PrietoGodinoLab/OptoPi/OptoPi V1/Photos/IMG_20220902_123817.jpg

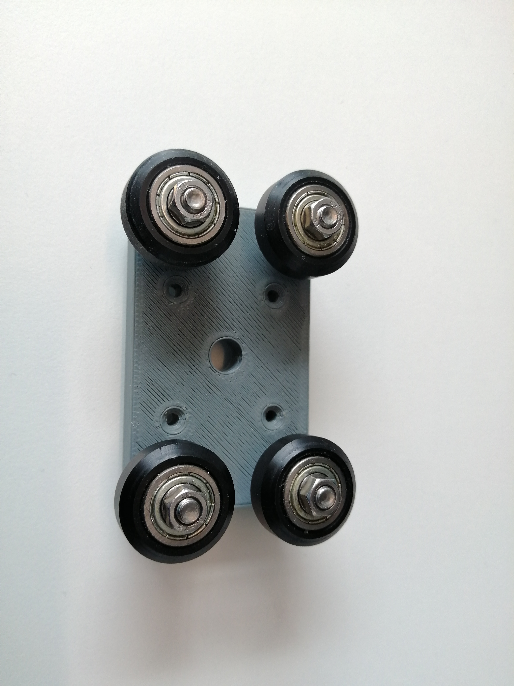
OptoPi V1/Photos/IMG_20220902_123817.jpg
