PrietoGodinoLab/OptoPi/OptoPi V1/Photos/IMG_20220902_124619.jpg

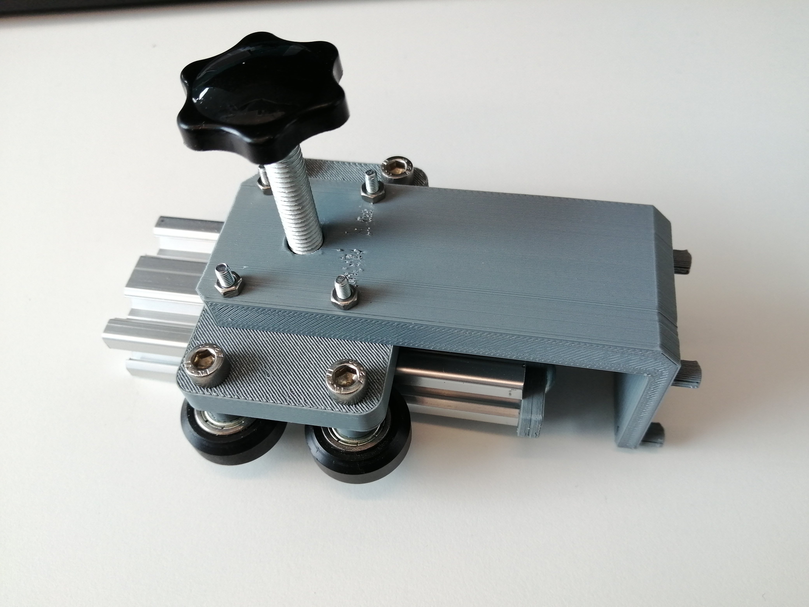
OptoPi V1/Photos/IMG_20220902_124619.jpg
