PrietoGodinoLab/OptoPi/OptoPi V1/Photos/IMG_20220927_121345.jpg

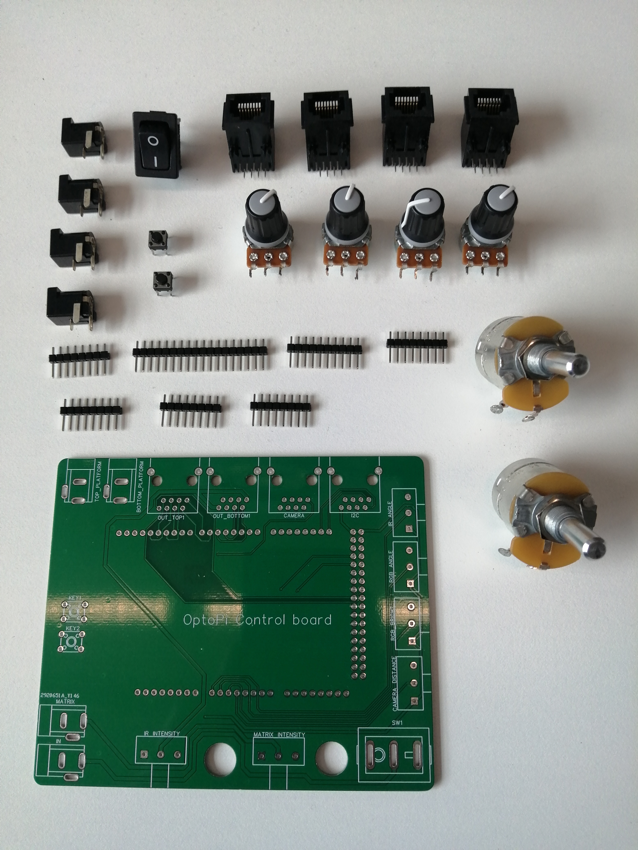
OptoPi V1/Photos/IMG_20220927_121345.jpg
