PrietoGodinoLab/OptoPi/OptoPi V1/Photos/IMG_20220929_140732.jpg

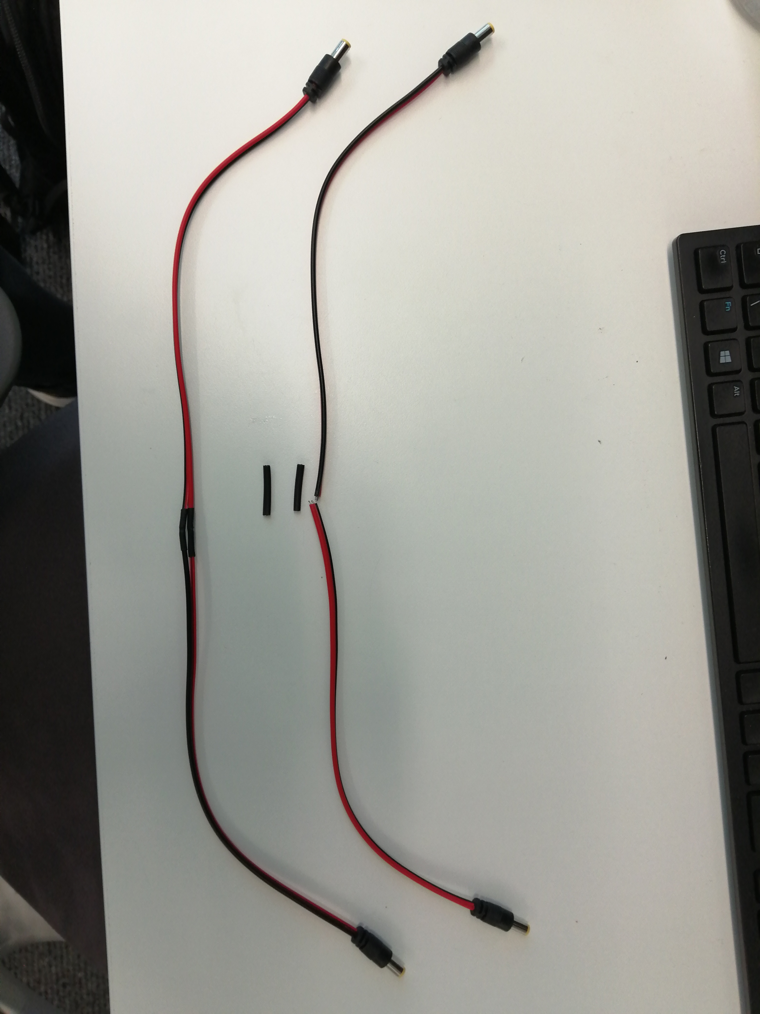
OptoPi V1/Photos/IMG_20220929_140732.jpg
