PrietoGodinoLab/OptoPi/OptoPi V1/Photos/IMG_20220929_161415.jpg

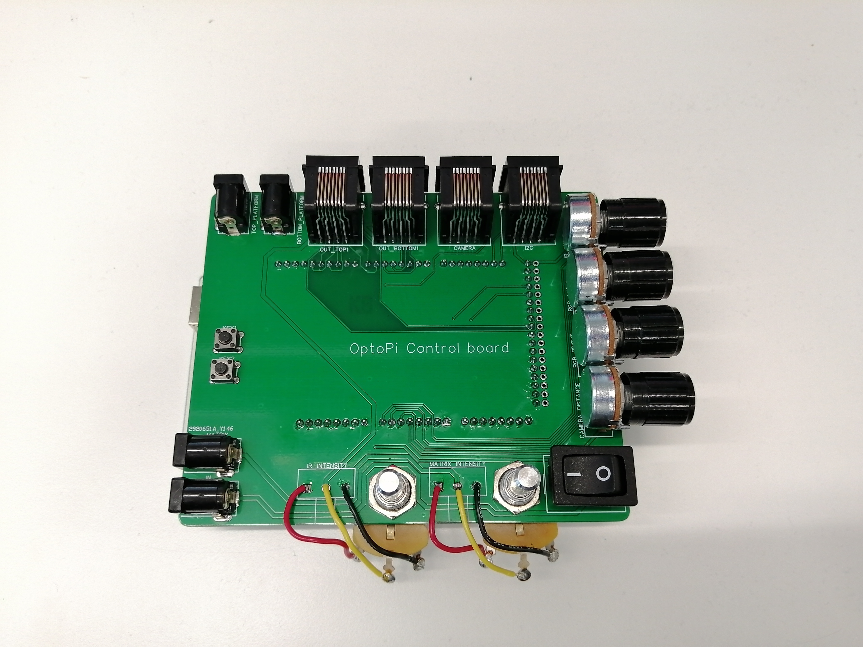
OptoPi V1/Photos/IMG_20220929_161415.jpg
