PrietoGodinoLab/OptoPi/OptoPi V1/Photos/IMG_20221003_110427.jpg

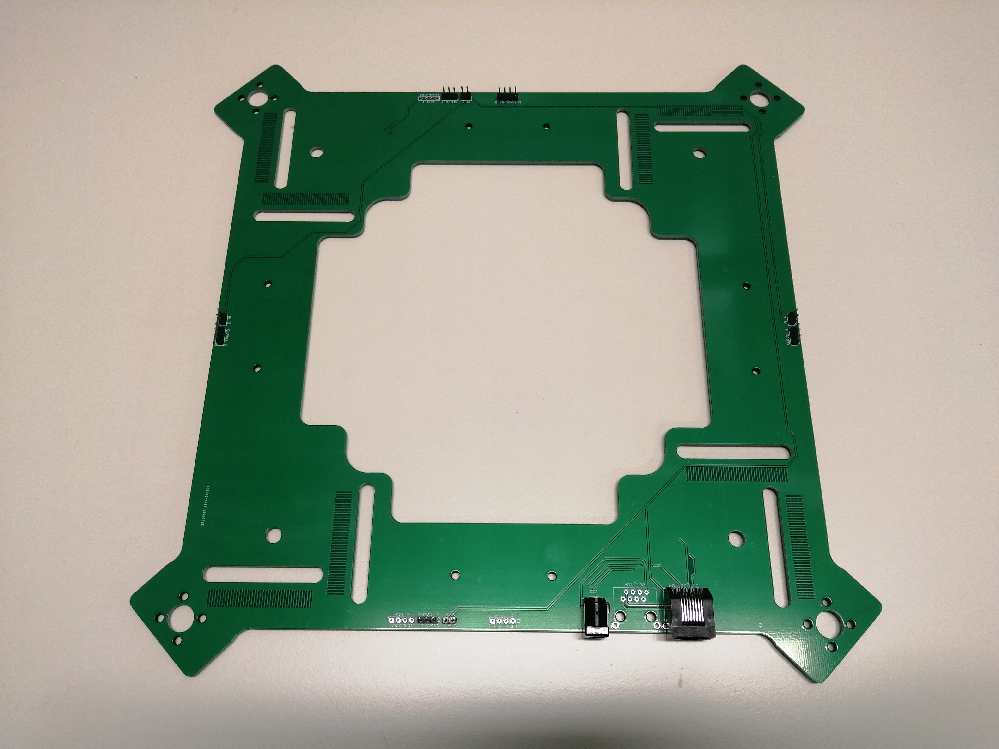
OptoPi V1/Photos/IMG_20221003_110427.jpg
