PrietoGodinoLab/OptoPi/OptoPi V1/Photos/IMG_20221003_110507.jpg

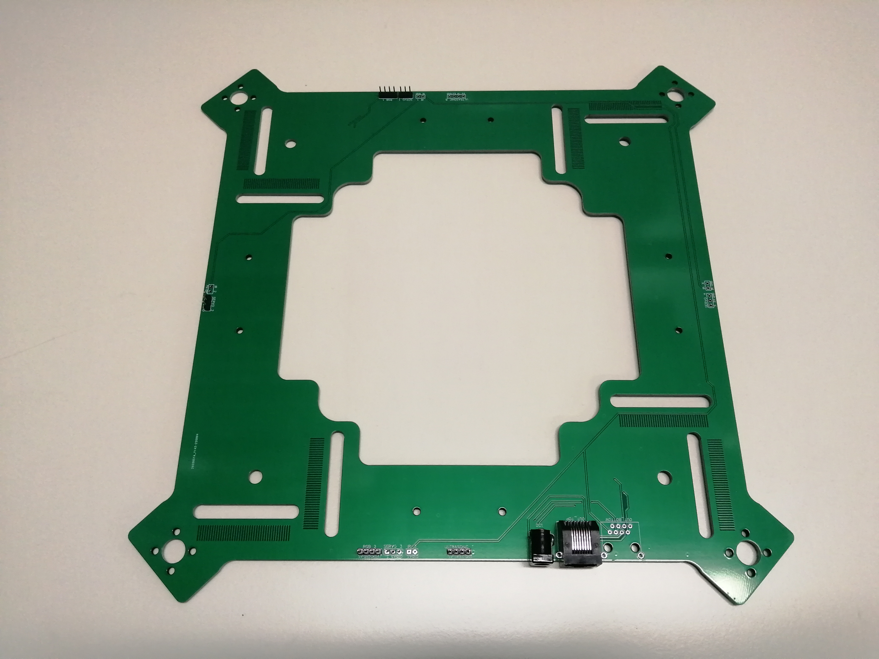
OptoPi V1/Photos/IMG_20221003_110507.jpg
