PrietoGodinoLab/OptoPi/OptoPi V1/Photos/IMG_20221003_115522.jpg

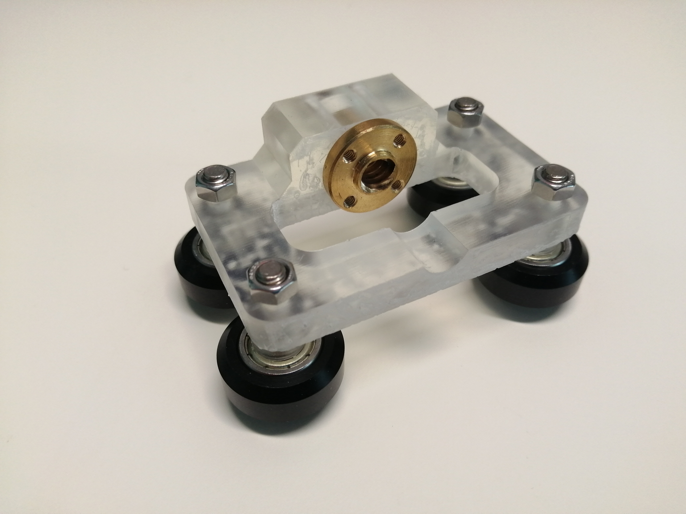
OptoPi V1/Photos/IMG_20221003_115522.jpg
