PrietoGodinoLab/OptoPi/OptoPi V1/Photos/IMG_20221003_143128.jpg

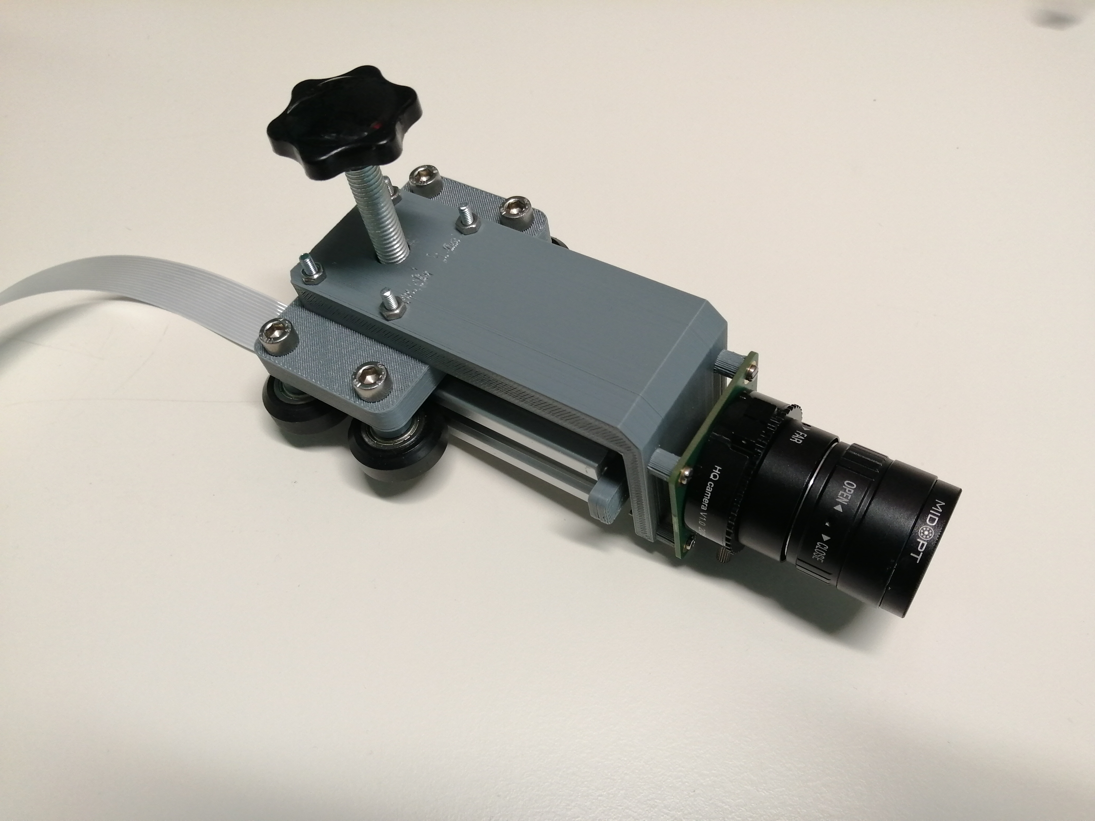
OptoPi V1/Photos/IMG_20221003_143128.jpg
