PrietoGodinoLab/OptoPi/OptoPi V1/Photos/IMG_20221003_161605.jpg

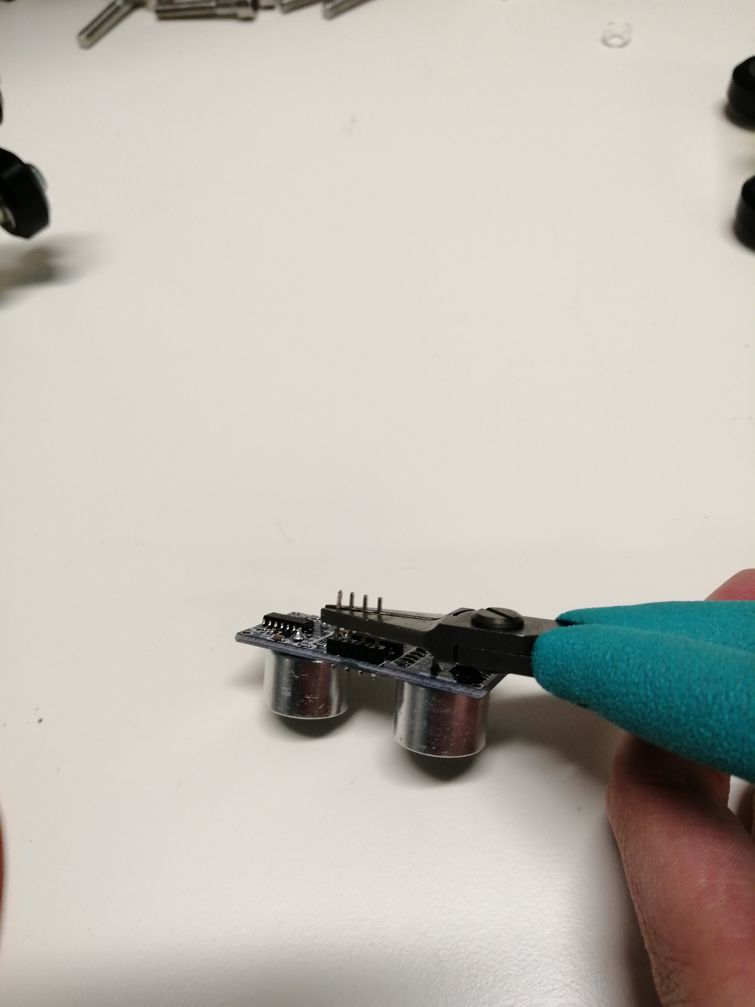
OptoPi V1/Photos/IMG_20221003_161605.jpg
