PrietoGodinoLab/OptoPi/OptoPi V1/Photos/IMG_20221004_111716.jpg

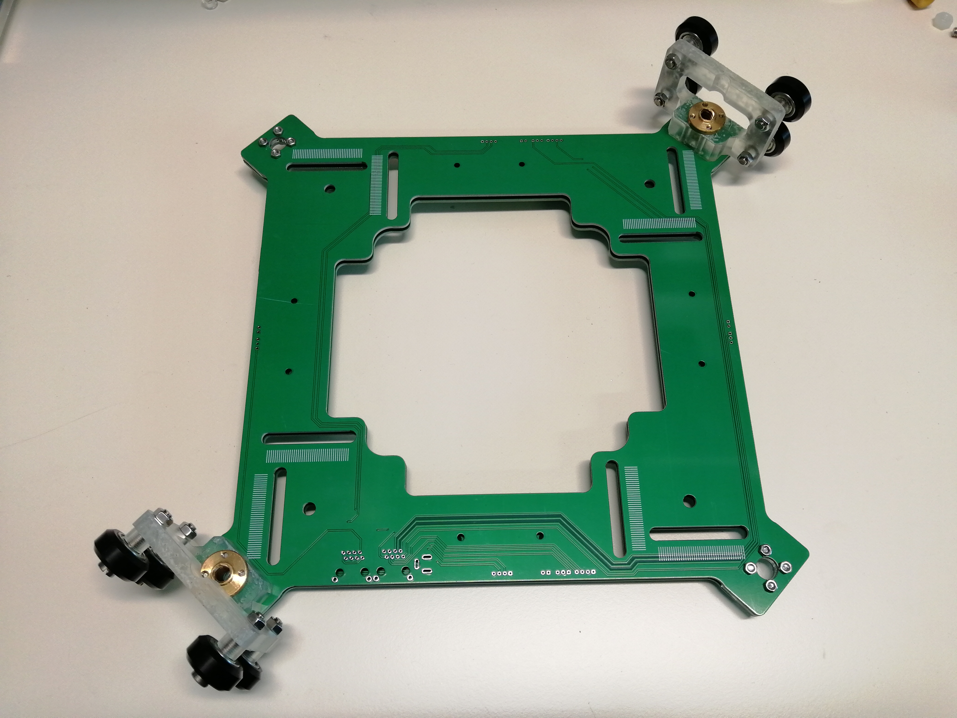
OptoPi V1/Photos/IMG_20221004_111716.jpg
