PrietoGodinoLab/OptoPi/OptoPi V1/Photos/IMG_20221004_111721_edit_144298494075898.jpg

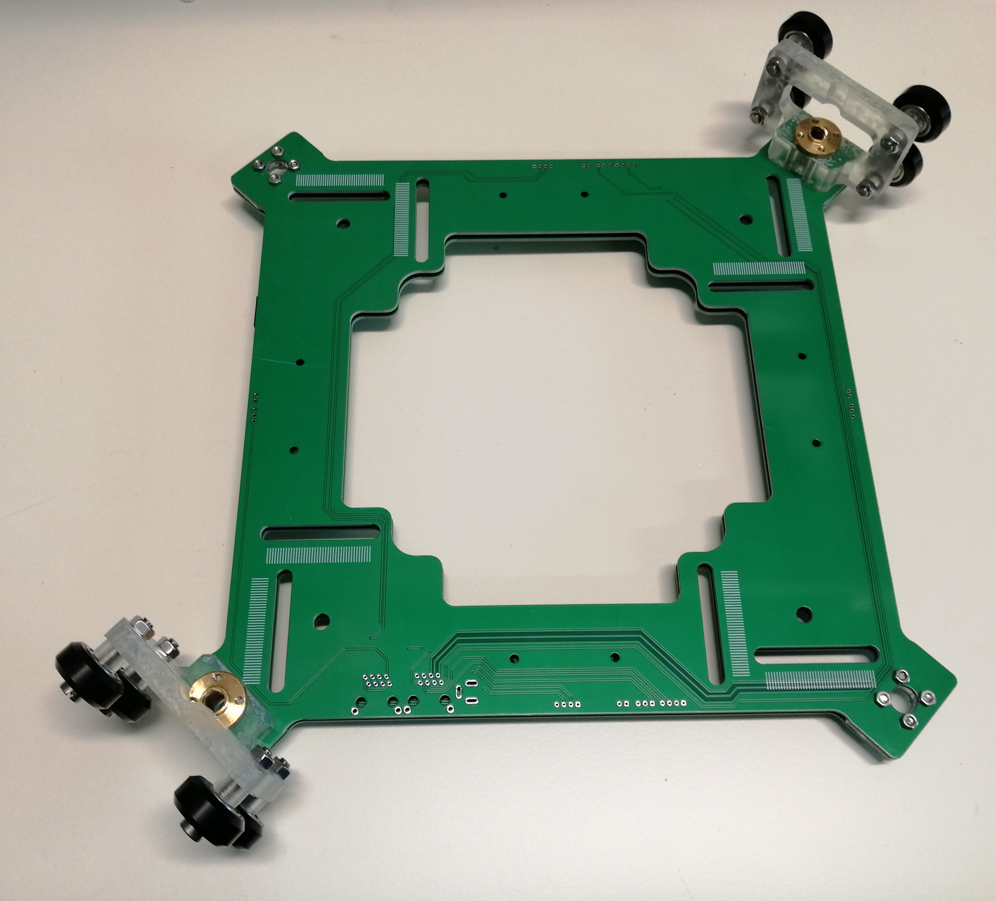
OptoPi V1/Photos/IMG_20221004_111721_edit_144298494075898.jpg
