PrietoGodinoLab/OptoPi/OptoPi V1/Photos/IMG_20221004_120927_edit_145196687061698.jpg

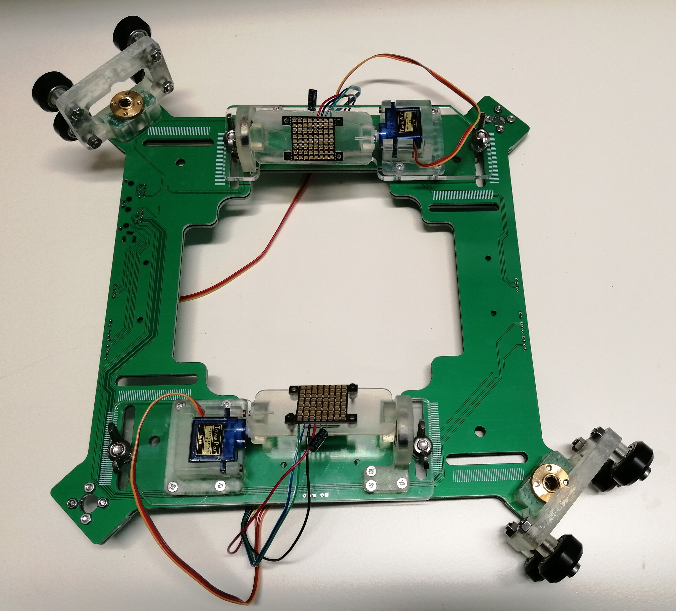
OptoPi V1/Photos/IMG_20221004_120927_edit_145196687061698.jpg
