PrietoGodinoLab/OptoPi/OptoPi V1/Photos/IMG_20221004_121041_edit_145273111731999.jpg

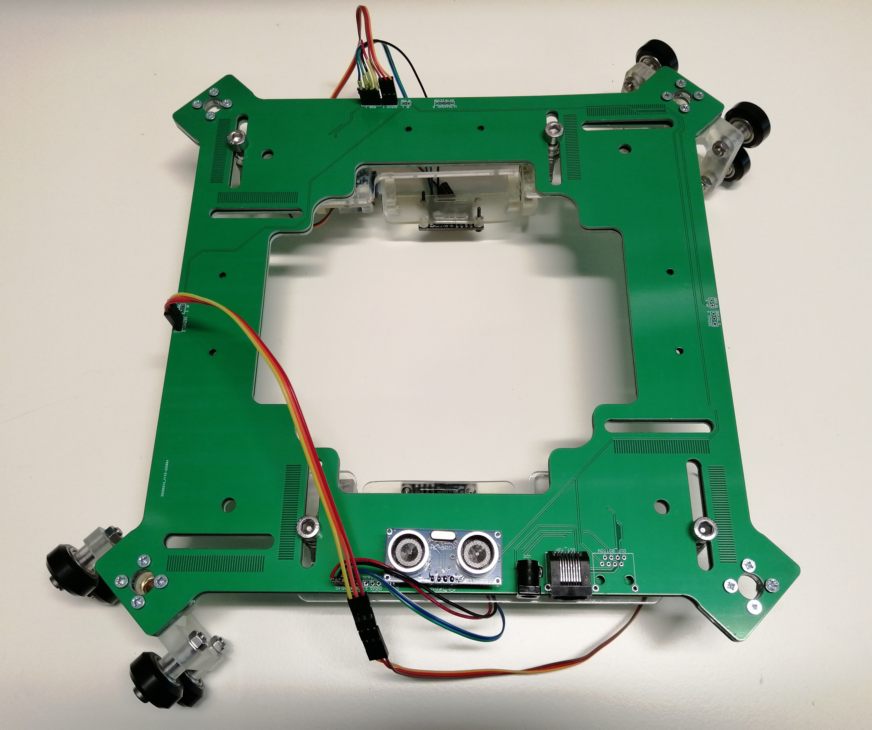
OptoPi V1/Photos/IMG_20221004_121041_edit_145273111731999.jpg
