PrietoGodinoLab/OptoPi/OptoPi V1/Photos/IMG_20221004_122243.jpg

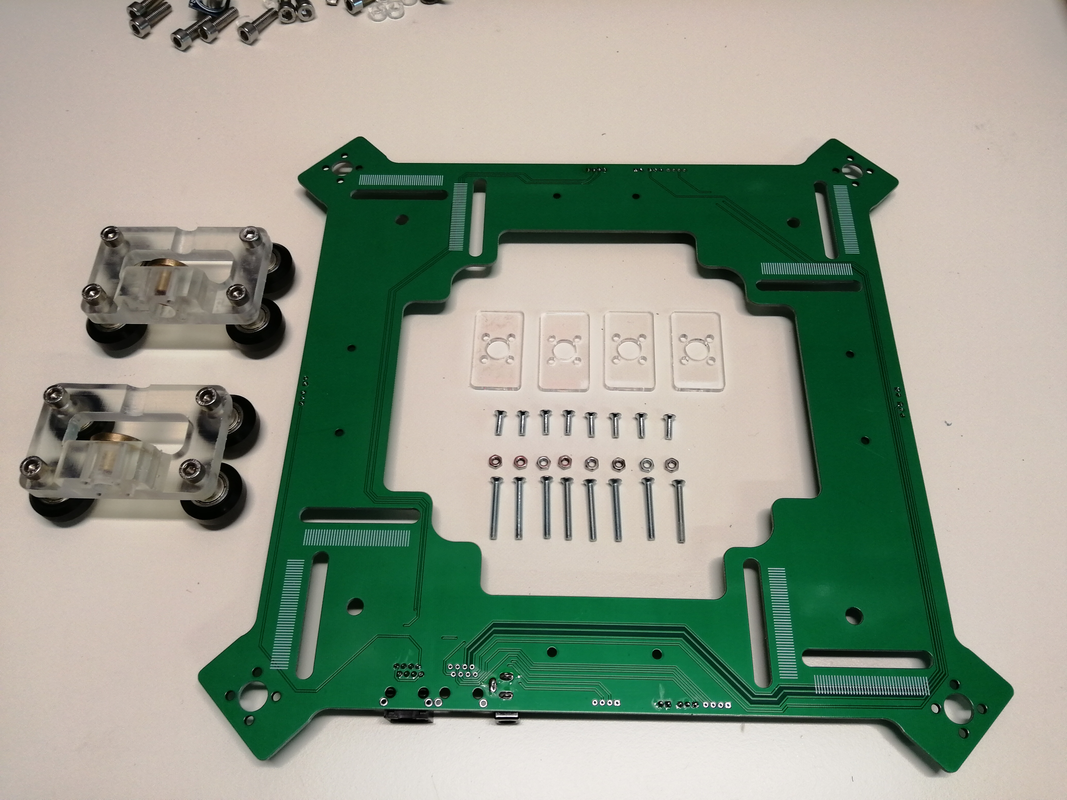
OptoPi V1/Photos/IMG_20221004_122243.jpg
