PrietoGodinoLab/OptoPi/OptoPi V1/Photos/IMG_20221004_122329_edit_145474023625718.jpg

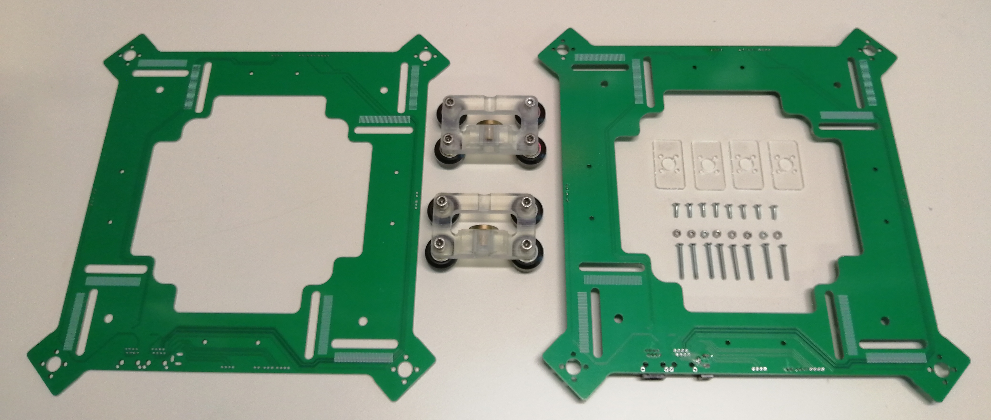
OptoPi V1/Photos/IMG_20221004_122329_edit_145474023625718.jpg
