PrietoGodinoLab/OptoPi/OptoPi V1/Photos/IMG_20221004_122958.jpg

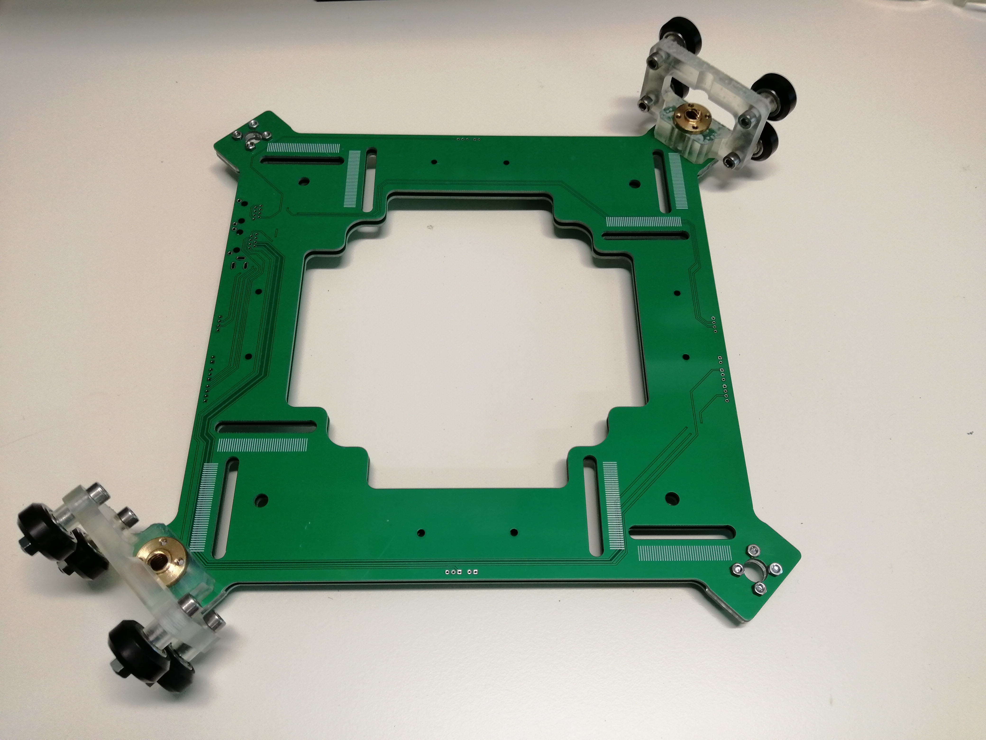
OptoPi V1/Photos/IMG_20221004_122958.jpg
