PrietoGodinoLab/OptoPi/OptoPi V1/Photos/IMG_20221004_123710.jpg

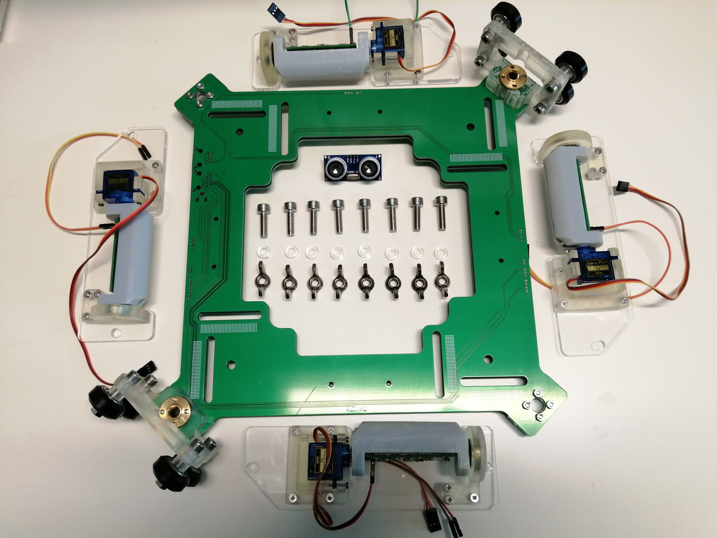
OptoPi V1/Photos/IMG_20221004_123710.jpg
