PrietoGodinoLab/OptoPi/OptoPi V1/Photos/IMG_20221004_131331_edit_146869959492172.jpg

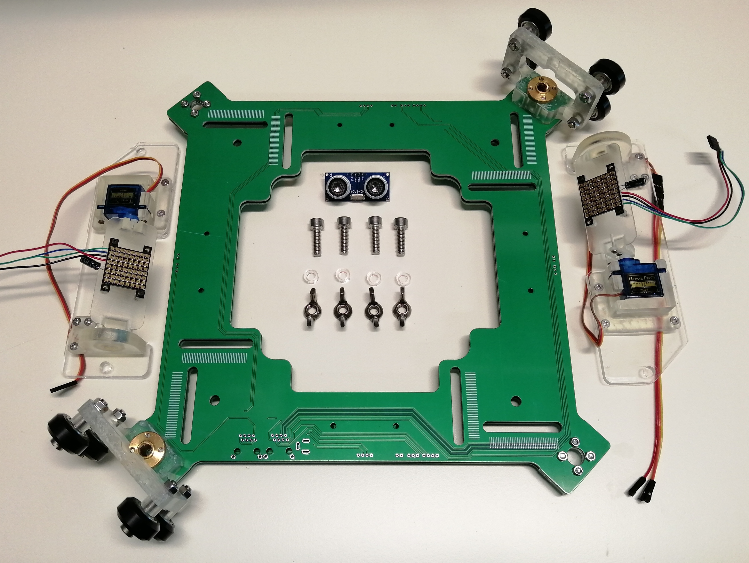
OptoPi V1/Photos/IMG_20221004_131331_edit_146869959492172.jpg
