PrietoGodinoLab/OptoPi/OptoPi V1/Photos/IMG_20221004_133414_edit_147019198305691.jpg

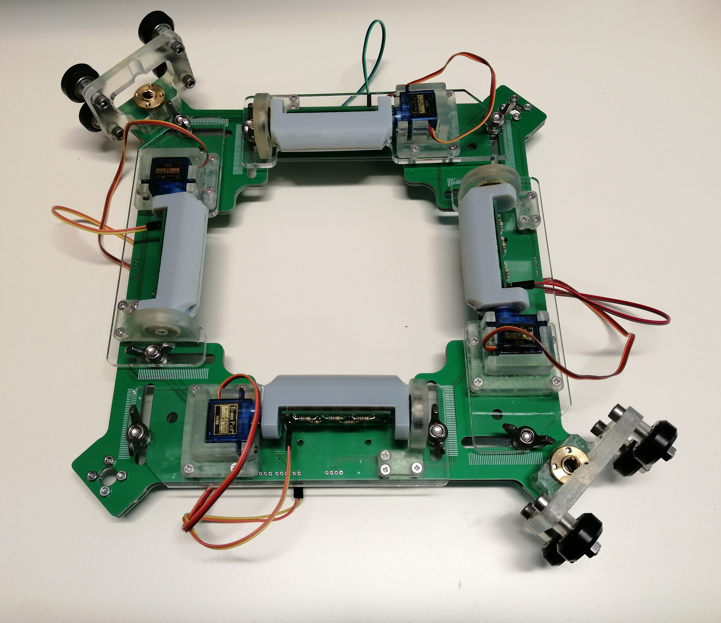
OptoPi V1/Photos/IMG_20221004_133414_edit_147019198305691.jpg
