PrietoGodinoLab/OptoPi/OptoPi V1/Photos/IMG_20221004_133534_edit_147065994163496.jpg

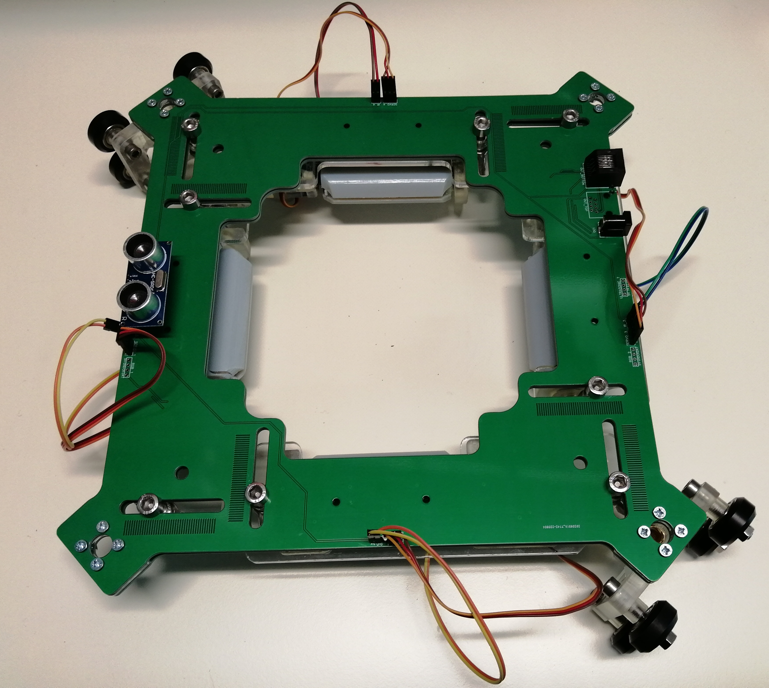
OptoPi V1/Photos/IMG_20221004_133534_edit_147065994163496.jpg
