PrietoGodinoLab/OptoPi/OptoPi V1/Photos/IMG_20221004_133632.jpg

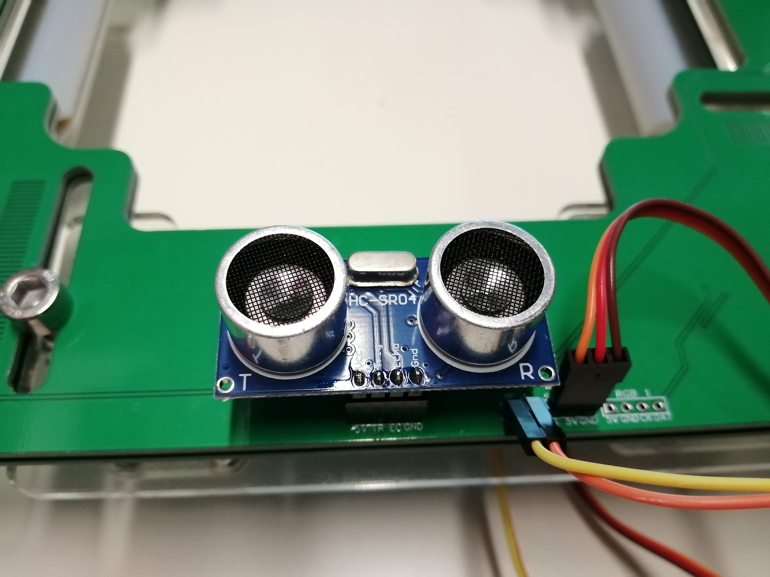
OptoPi V1/Photos/IMG_20221004_133632.jpg
