PrietoGodinoLab/OptoPi/OptoPi V1/Photos/IMG_20221005_123752.jpg

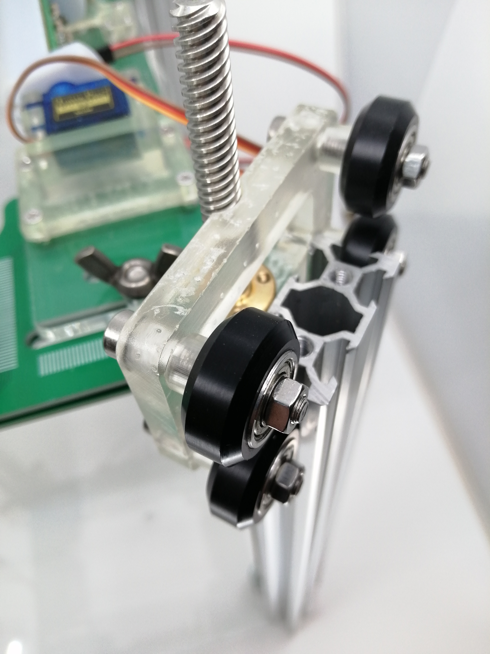
OptoPi V1/Photos/IMG_20221005_123752.jpg
