PrietoGodinoLab/OptoPi/OptoPi V1/Photos/IMG_20221005_123757.jpg

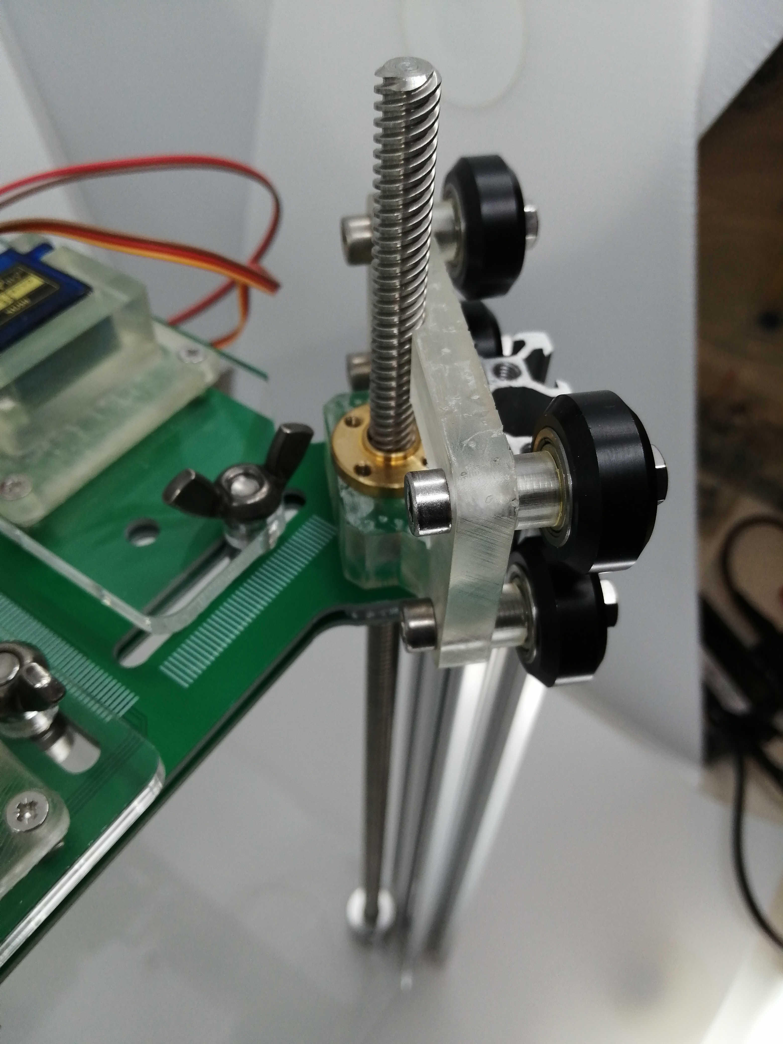
OptoPi V1/Photos/IMG_20221005_123757.jpg
