PrietoGodinoLab/OptoPi/OptoPi V1/Photos/IMG_20221005_123804.jpg

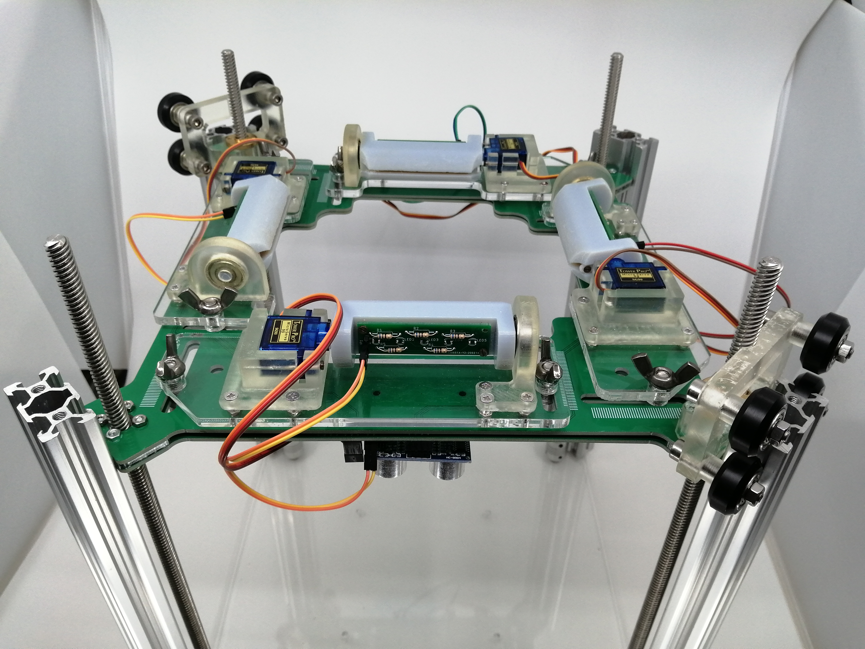
OptoPi V1/Photos/IMG_20221005_123804.jpg
