PrietoGodinoLab/OptoPi/OptoPi V1/Photos/IMG_20221005_123850.jpg

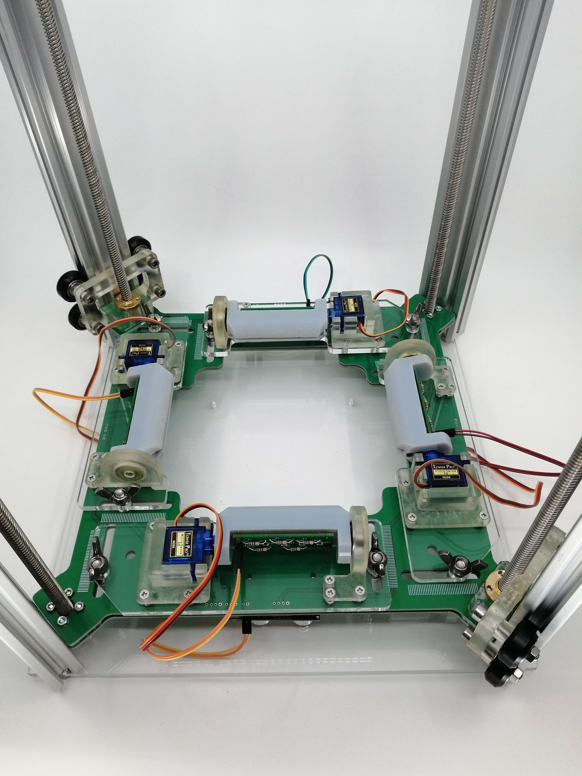
OptoPi V1/Photos/IMG_20221005_123850.jpg
