PrietoGodinoLab/OptoPi/OptoPi V1/Photos/IMG_20221005_124210.jpg

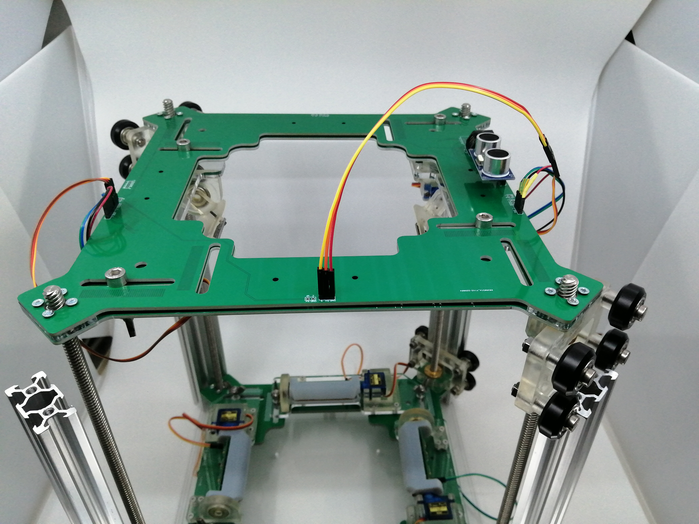
OptoPi V1/Photos/IMG_20221005_124210.jpg
