PrietoGodinoLab/OptoPi/OptoPi V1/Photos/IMG_20221005_124215.jpg

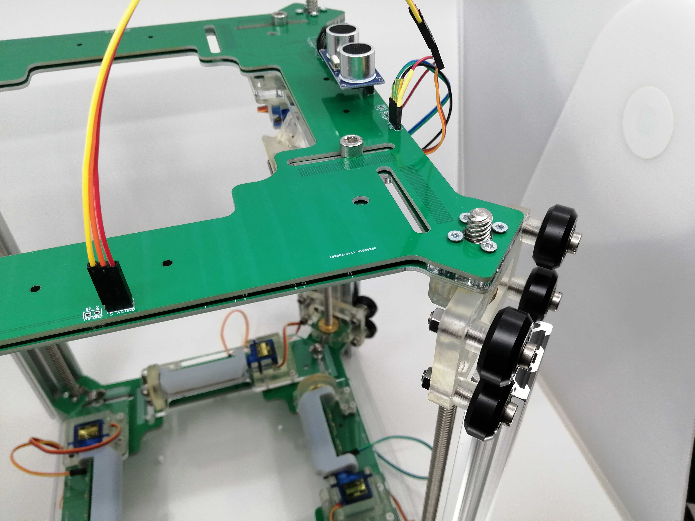
OptoPi V1/Photos/IMG_20221005_124215.jpg
