PrietoGodinoLab/OptoPi/OptoPi V1/Photos/IMG_20221005_124533.jpg

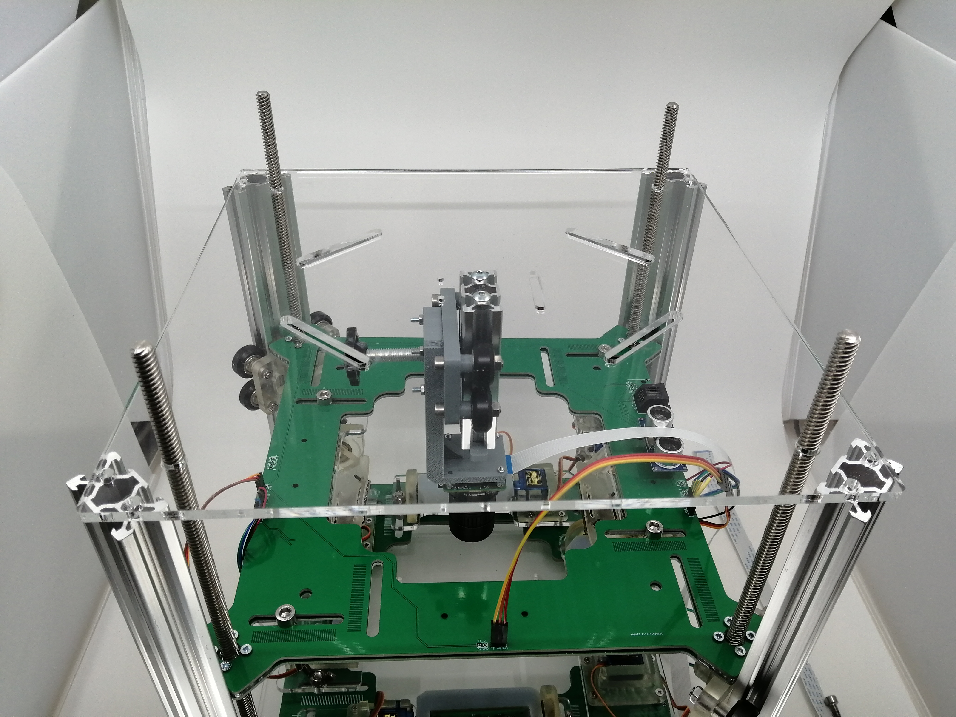
OptoPi V1/Photos/IMG_20221005_124533.jpg
