PrietoGodinoLab/OptoPi/OptoPi V1/Photos/IMG_20221005_124552.jpg

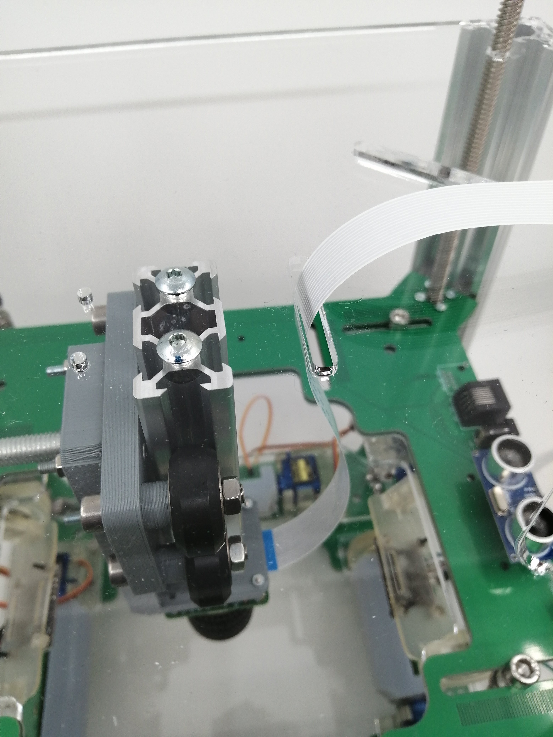
OptoPi V1/Photos/IMG_20221005_124552.jpg
