PrietoGodinoLab/OptoPi/OptoPi V1/Photos/IMG_20221005_124958.jpg

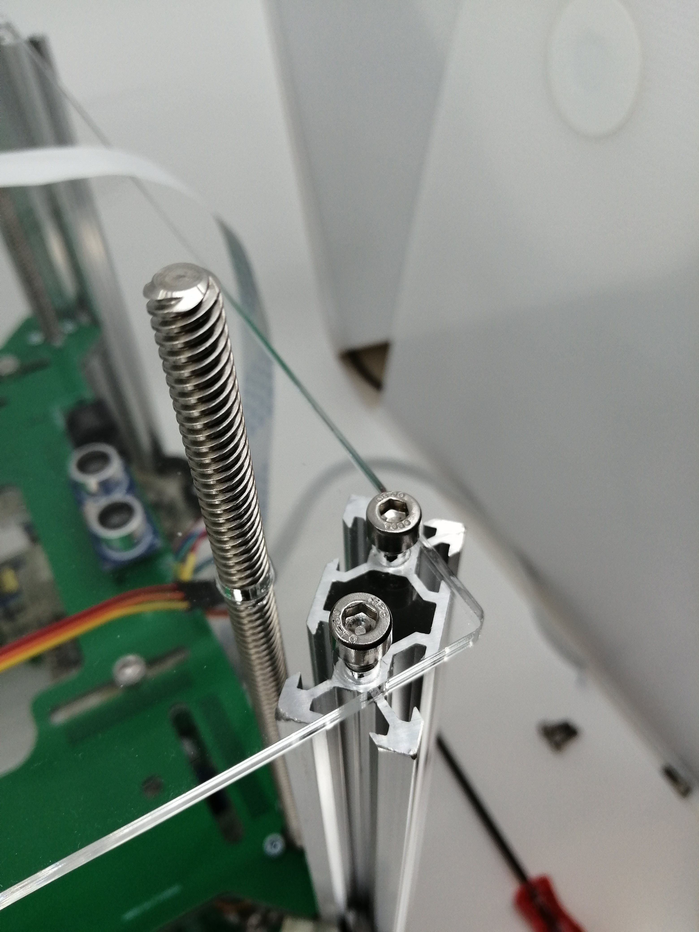
OptoPi V1/Photos/IMG_20221005_124958.jpg
