PrietoGodinoLab/OptoPi/OptoPi V1/Photos/IMG_20221005_125000.jpg

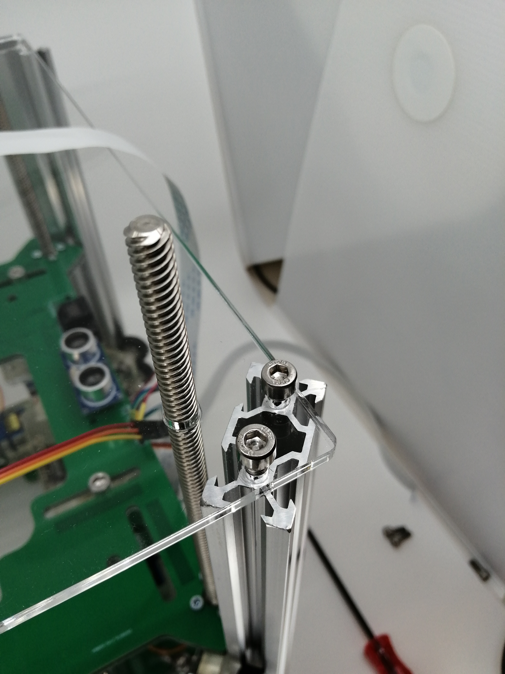
OptoPi V1/Photos/IMG_20221005_125000.jpg
