PrietoGodinoLab/OptoPi/OptoPi V1/Photos/IMG_20221005_125309.jpg

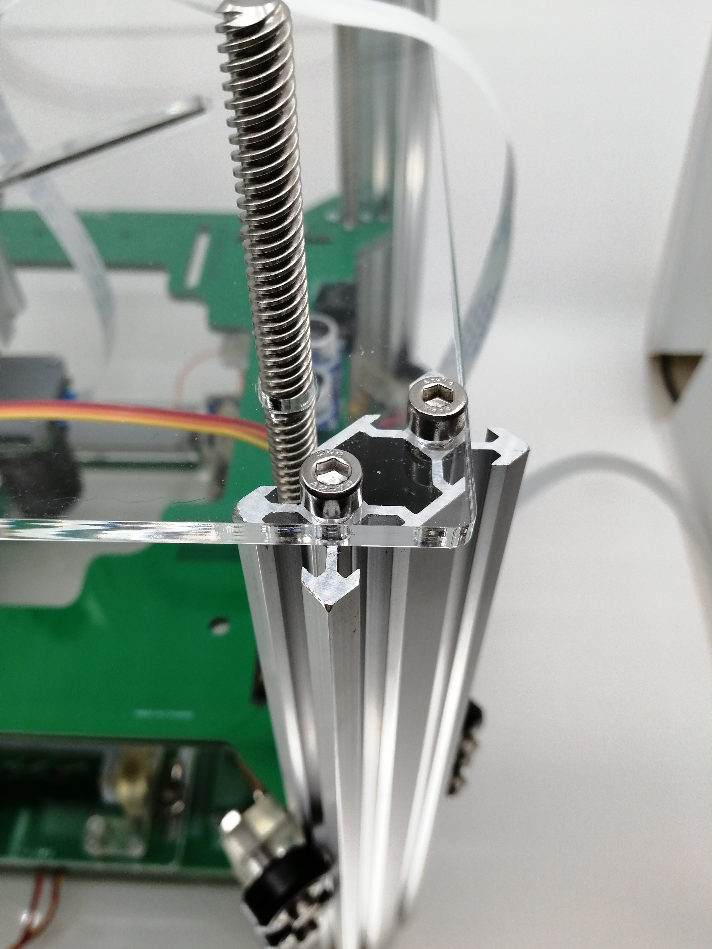
OptoPi V1/Photos/IMG_20221005_125309.jpg
