PrietoGodinoLab/OptoPi/OptoPi V1/Photos/IMG_20221005_130104.jpg

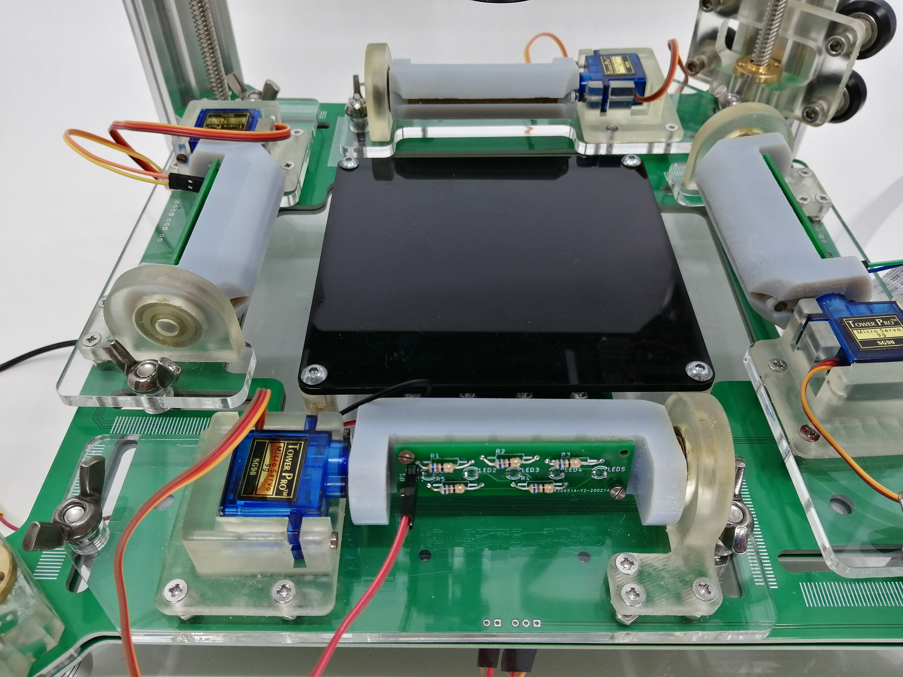
OptoPi V1/Photos/IMG_20221005_130104.jpg
