PrietoGodinoLab/OptoPi/OptoPi V1/Photos/IMG_20221005_143917.jpg

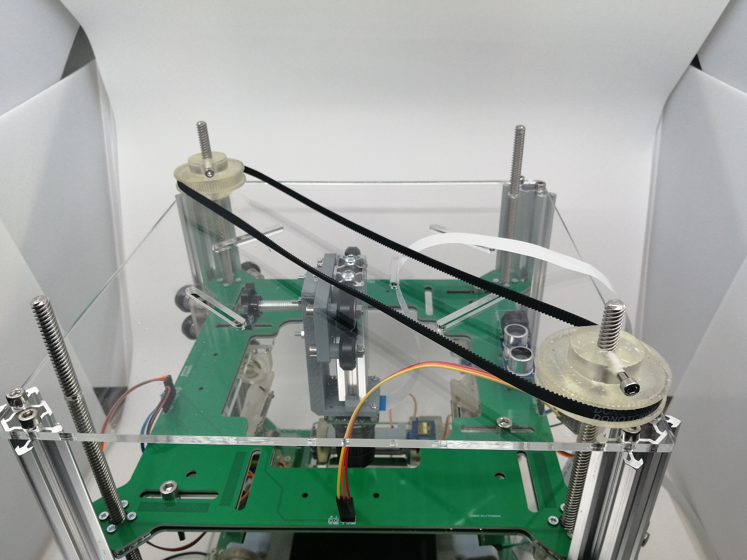
OptoPi V1/Photos/IMG_20221005_143917.jpg
