PrietoGodinoLab/OptoPi/OptoPi V1/Photos/IMG_20221005_143921.jpg

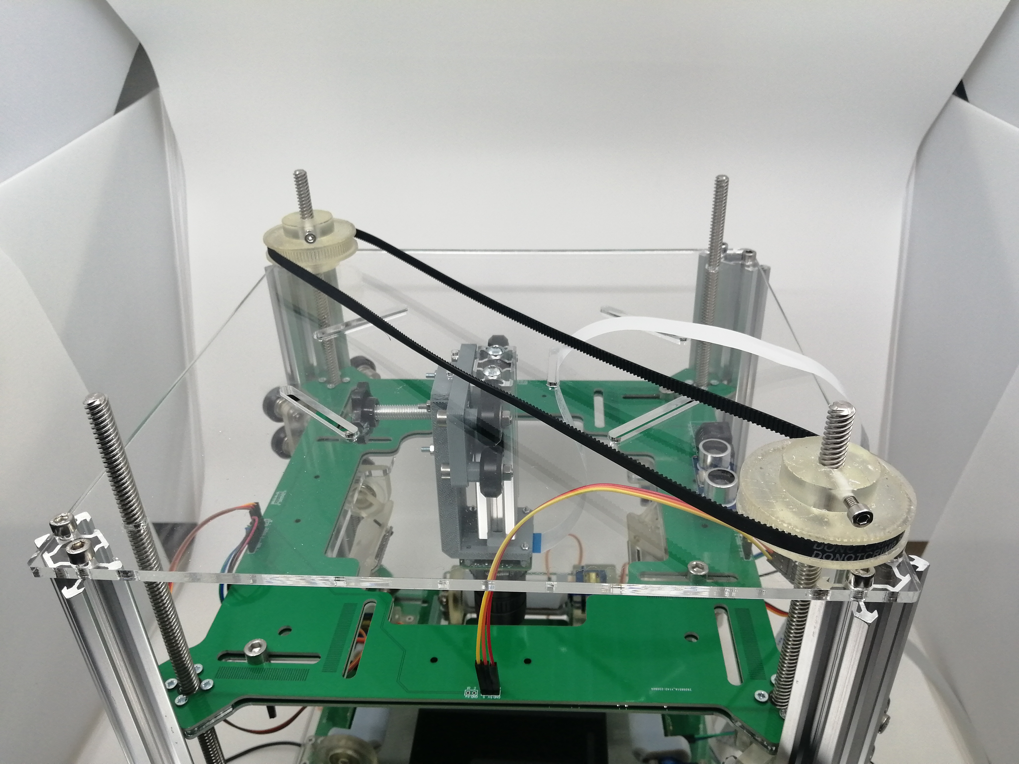
OptoPi V1/Photos/IMG_20221005_143921.jpg
