PrietoGodinoLab/OptoPi/OptoPi V1/Photos/IMG_20221005_144141.jpg

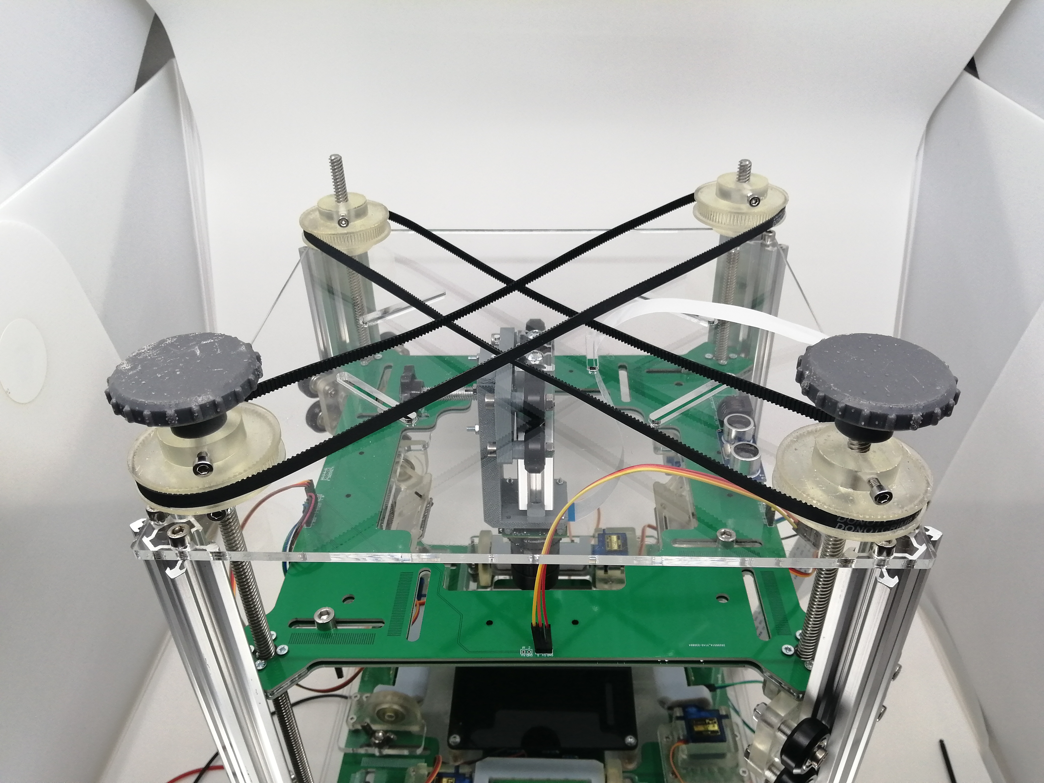
OptoPi V1/Photos/IMG_20221005_144141.jpg
