PrietoGodinoLab/OptoPi/OptoPi V1/Photos/IMG_20221005_145353.jpg

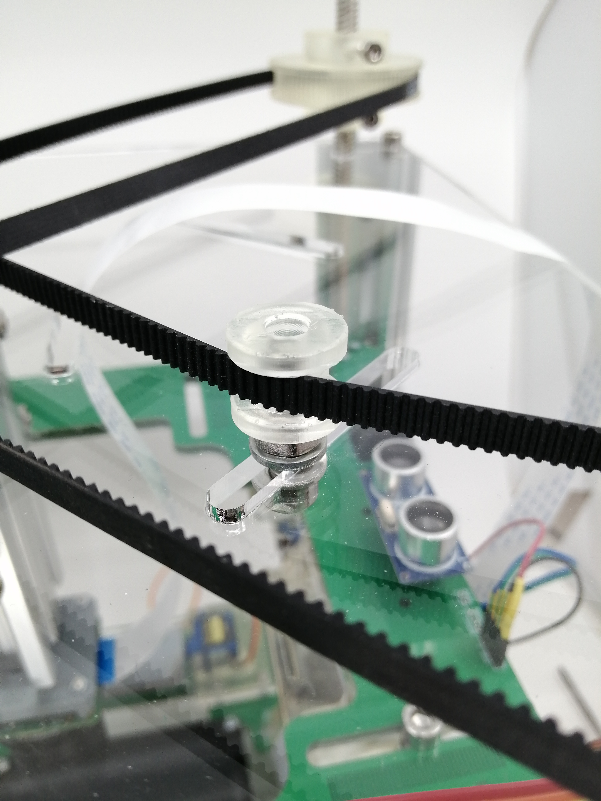
OptoPi V1/Photos/IMG_20221005_145353.jpg
