PrietoGodinoLab/OptoPi/OptoPi V1/Photos/IMG_20221005_145714.jpg

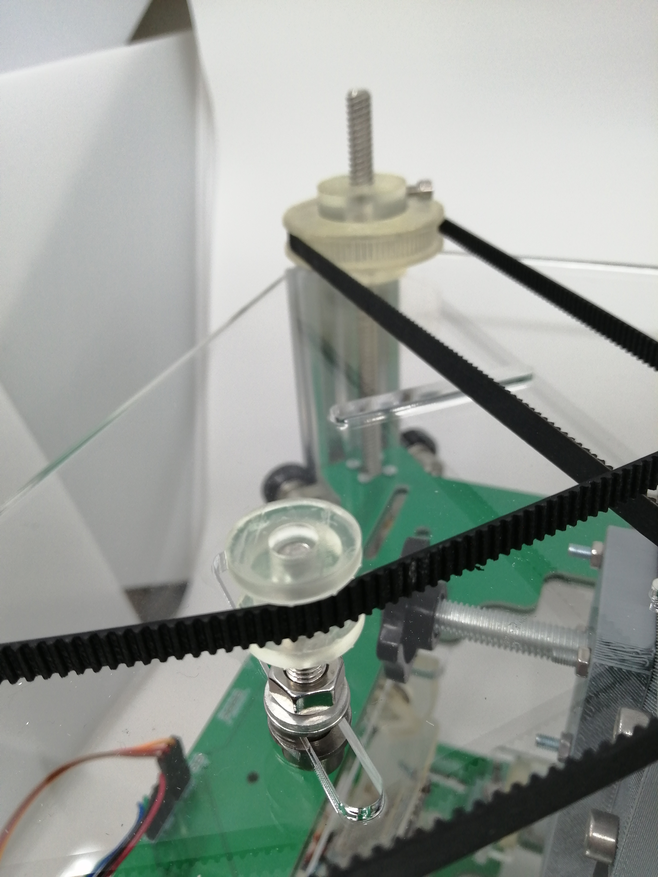
OptoPi V1/Photos/IMG_20221005_145714.jpg
