PrietoGodinoLab/OptoPi/OptoPi V1/Photos/IMG_20221005_152950.jpg

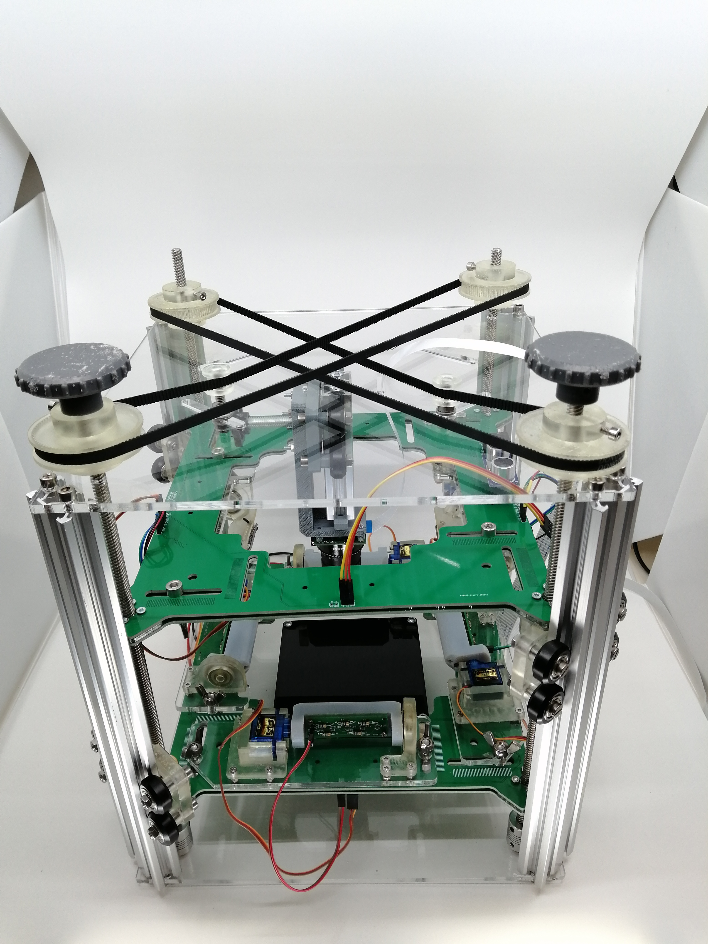
OptoPi V1/Photos/IMG_20221005_152950.jpg
