PrietoGodinoLab/OptoPi/OptoPi V1/Photos/IMG_20221005_154532.jpg

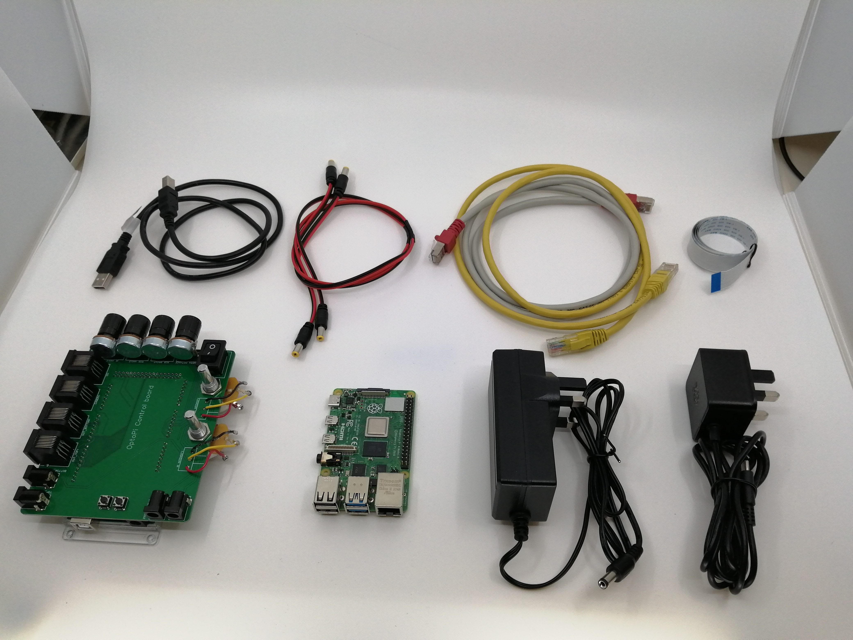
OptoPi V1/Photos/IMG_20221005_154532.jpg
