PrietoGodinoLab/OptoPi/OptoPi V1/Photos/IMG_20221005_164253.jpg

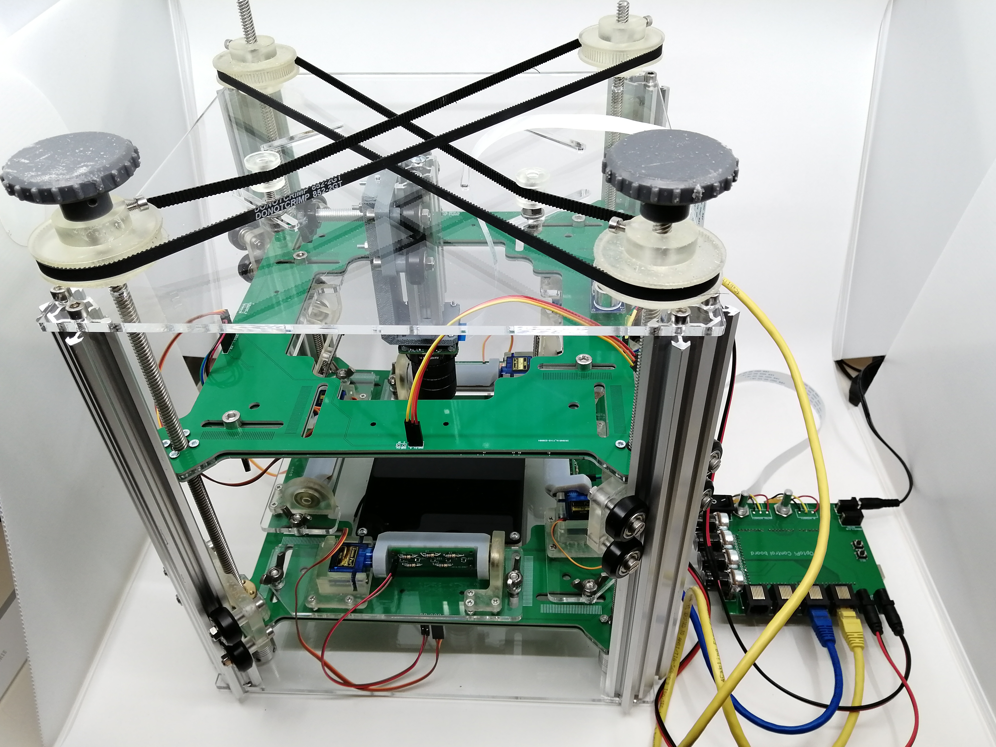
OptoPi V1/Photos/IMG_20221005_164253.jpg
