PrietoGodinoLab/OptoPi/OptoPi V1/Photos/IMG_20221005_164258.jpg

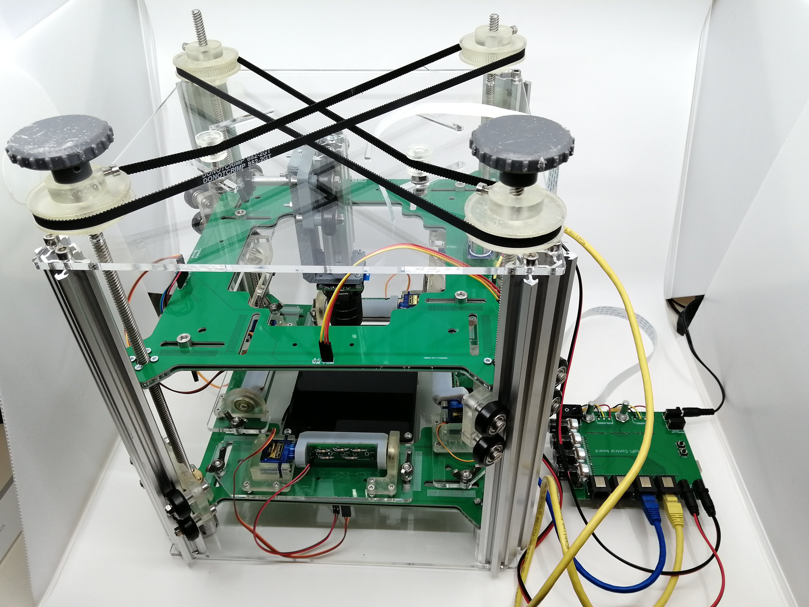
OptoPi V1/Photos/IMG_20221005_164258.jpg
