PrietoGodinoLab/OptoPi/OptoPi V1/Photos/IMG_20221006_125143.jpg

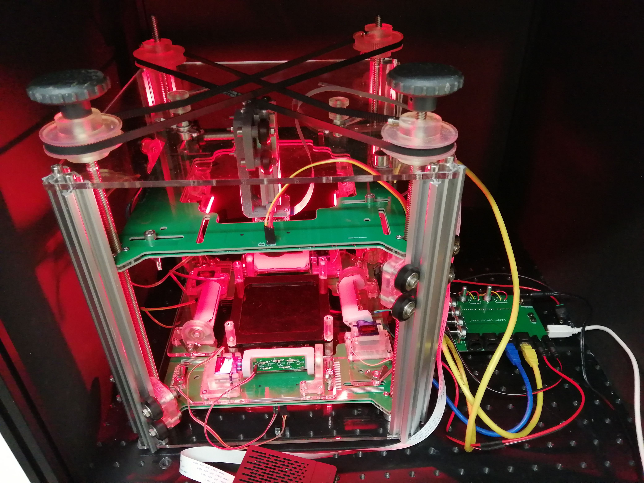
OptoPi V1/Photos/IMG_20221006_125143.jpg
