PrietoGodinoLab/OptoPi/Supplementary/visual_distortion_correction/check_pattern.png

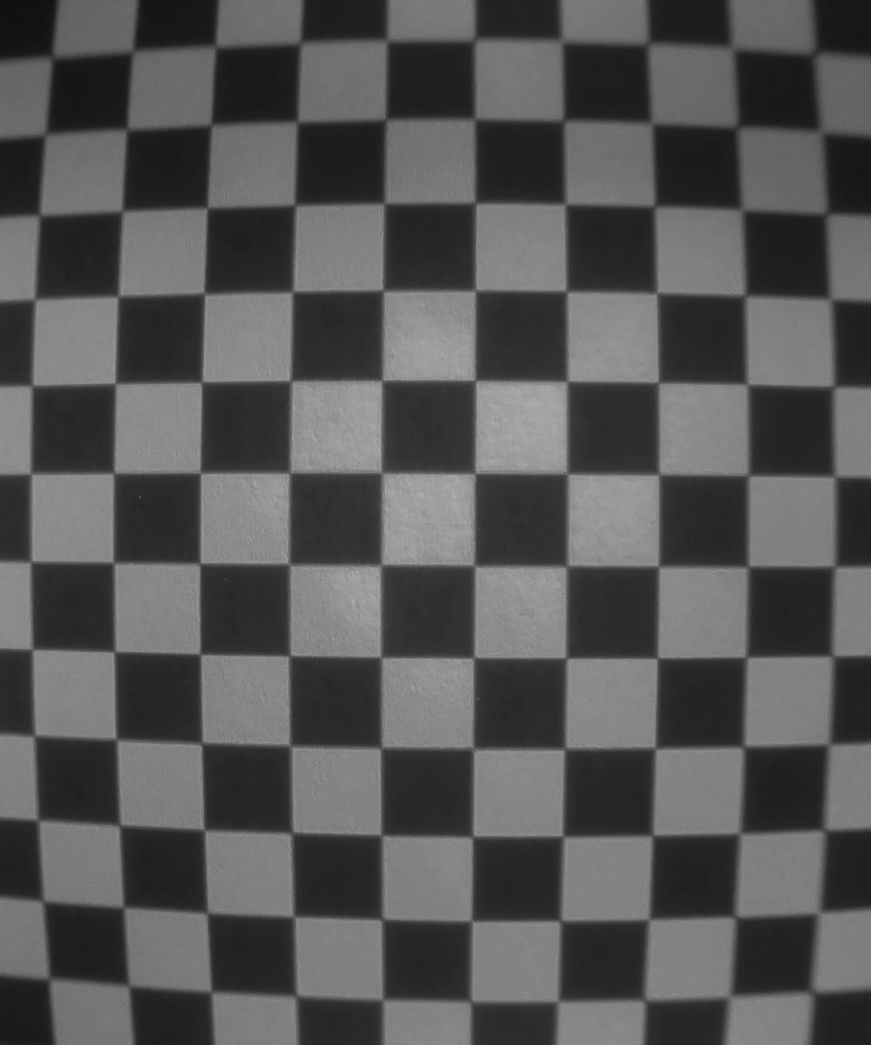
Supplementary/visual_distortion_correction/check_pattern.png
